juanjorojash/cell_tester_public/charger_discharger.h

/**
 * @file charger_discharger.h
 * @author Juan J. Rojas
 * @date 7 Aug 2018
 * @brief State machine header file for Charge and Discharge System.
 * @par Institution:
 * LaSEINE / CeNT. Kyushu Institute of Technology.
 * @par Mail (after leaving Kyutech):
 * juan.rojas@tec.ac.cr
 * @par Git repository:
 * https://bitbucket.org/juanjorojash/cell_charger_discharger
 */

#ifndef CHARGER_DISCHARGER_H
    #define CHARGER_DISCHARGER_H
    // PIC16F1786 Configuration Bit Settings

    // 'C' source line config statements
    #pragma config FOSC = INTOSC    // Oscillator Selection (INTOSC oscillator: I/O function on CLKIN pin)
    #pragma config WDTE = OFF       // Watchdog Timer Disabled (WDT disabled)
    #pragma config PWRTE = OFF      // Power-up Timer Enable (PWRT disabled)
    #pragma config MCLRE = ON       // MCLR Pin Function Select (MCLR/VPP pin function is MCLR)//If this is enabled, the Timer0 module will not work properly.
    #pragma config CP = OFF         // Flash Program Memory Code Protection (Program memory code protection is disabled)
    #pragma config CPD = OFF        // Data Memory Code Protection (Data memory code protection is disabled)
    #pragma config BOREN = OFF      // Brown-out Reset Enable (Brown-out Reset enabled)
    #pragma config CLKOUTEN = ON    // Clock Out Negative Enable (CLKOUT function is disabled. I/O or oscillator function on the CLKOUT pin)
    #pragma config IESO = ON        // Internal/External Switchover (Internal/External Switchover mode is enabled)
    #pragma config FCMEN = ON       // Fail-Safe Clock Monitor Enable (Fail-Safe Clock Monitor is enabled)

    // CONFIG2
    #pragma config WRT = OFF        // Flash Memory Self-Write Protection (Write protection off)
    #pragma config VCAPEN = OFF     // Voltage Regulator Capacitor Enable bit (Vcap functionality is disabled on RA6.)
    #pragma config PLLEN = OFF      // PLL Enable (4x PLL disabled)
    #pragma config STVREN = ON      // Stack Overflow/Underflow Reset Enable (Stack Overflow or Underflow will cause a Reset)
    #pragma config BORV = LO        // Brown-out Reset Voltage Selection (Brown-out Reset Voltage (Vbor), low trip point selected.)
    #pragma config LPBOR = OFF      // Low Power Brown-Out Reset Enable Bit (Low power brown-out is disabled)
    #pragma config LVP = OFF        // Low-Voltage Programming Enable (Low-voltage programming disabled)//IF THIS IN ON MCLR is always enabled

    #include <xc.h>
    #include <stdio.h>
    #include <stdlib.h>
    #include <math.h>
    #include <stdint.h> // To include uint8_t and uint16_t
    #include <string.h>
    #include <stdbool.h> // Include bool type
    /** This is the State Machine enum*/
	enum states { 
        STANDBY = 0, ///< "Stand by" state, defined by function @link fSTANDBY() @endlink
        IDLE = 1, ///< "Idle" state, defined by function @link fIDLE() @endlink
        FAULT = 2, ///< "Fault" state, defined by function @link fFAULT() @endlink
        ISDONE = 3, ///< "Is done" state, defined by function @link fISDONE() @endlink
        WAIT = 4, ///< "Wait" state, defined by function @link fWAIT() @endlink
        PREDISCHARGE = 5, ///< "Predischarge" state, defined by function @link fDISCHARGE() @endlink
        CHARGE = 6, ///< "Charge" state, defined by function @link fCHARGE() @endlink
        DISCHARGE = 7, ///< "Discharge" state, defined by function @link fDISCHARGE() @endlink
        POSTCHARGE = 8, ///< "Postcharge" state, defined by function @link fCHARGE() @endlink
        DS_DC_res = 9, ///< "Discharged state DC resistance" state, defined by function @link fDC_res() @endlink
        CS_DC_res = 10, ///< "Charged state DC resistance" state, defined by function @link fDC_res() @endlink
        PS_DC_res = 11 ///< "Postcharged state DC resistance" state, defined by function @link fDC_res() @endlink
    };    
    void fSTANDBY(void);
    void fIDLE(void);
    void fCHARGE(void);
    void fDISCHARGE(void);
    void fDC_res(void);
    void fWAIT(void);
    void fISDONE(void);
    void fFAULT(void);
    void start_state_machine(void);
    void state_machine(void);
    void param(void);
    void converter_settings(void);
    void initialize(void);
    void pid(uint16_t feedback, uint16_t setpoint, int24_t* acum, uint16_t* duty_cycle);
    void set_DC(uint16_t* duty_cycle);
    uint16_t read_ADC(uint16_t channel);
    void scaling(void);
    void log_control(void);
    void display_value_u(uint16_t value);
    void display_value_s(int16_t value);
    void cc_cv_mode(uint16_t current_voltage, uint16_t reference_voltage, bool CC_mode_status);
    void control_loop(void);
    void calculate_avg(void);
    void interrupt_enable(void);
    void UART_send_char(char bt);
    char UART_get_char(void); 
    void UART_send_string(char* st_pt);
    void temp_protection(void);
    void Cell_ON(void);
    void Cell_OFF(void);
    void timing(void);
    #define     _XTAL_FREQ              32000000 ///< Frequency to coordinate delays, 32 MHz
    #define     ERR_MAX                 1000 ///< Maximum permisible error, useful to avoid ringing
    #define     ERR_MIN                 -1000 ///< Minimum permisible error, useful to avoid ringing
    #define     V_CHAN                  0b01010 ///< Definition of ADC channel for voltage measurements. AN10(RB1) 
    #define     I_CHAN                  0b01100 ///< Definition of ADC channel for current measurements. AN12(RB0)
    #define     T_CHAN                  0b00100 ///< Definition of ADC channel for temperature measurements. AN4(RA5)
    #define     CELL1_ON()              { RB2 = 1; } ///< Turn on Cell #1
    #define     CELL2_ON()              { RB3 = 1; } ///< Turn on Cell #2
    #define     CELL3_ON()              { RB4 = 1; } ///< Turn on Cell #3
    #define     CELL4_ON()              { RB5 = 1; } ///< Turn on Cell #4
    #define     CELL1_OFF()             { RB2 = 0; } ///< Turn off Cell #1
    #define     CELL2_OFF()             { RB3 = 0; } ///< Turn off Cell #2
    #define     CELL3_OFF()             { RB4 = 0; } ///< Turn off Cell #3
    #define     CELL4_OFF()             { RB5 = 0; } ///< Turn off Cell #4
    #define     AD_SET_CHAN(x)          { ADCON0bits.CHS = x; __delay_us(5); } ///< Set the ADC channel to @p x and wait for 5 microseconds.
    #define     AD_CONVERT()            { GO_nDONE = 1; while(GO_nDONE);} ///< Start the conversion and wait until it is finished
    #define     AD_RESULT()             { ad_res = 0; ad_res = (ADRESL & 0xFF)|((ADRESH << 8) & 0xF00);} ///< Store conversion result in #ad_res
    /** @brief Stop the converter*/
    /** Set @p conv to zero, turn off the main relay (@p RC5), set the duty cycle in @p DC_MIN, 
    turn off all the cell relays in the switcher board, disable the logging of data to the terminal 
    and the UART reception interrupts.
    */
    #define     STOP_CONVERTER()        { RC3 = 0; RC4 = 0; conv = 0; RC5 = 0; dc = DC_MIN; set_DC(&dc); Cell_OFF(); LOG_OFF();}
    #define     UART_INT_ON()           { while(RCIF) clear = RC1REG; RCIE = 1; } ///< Clear transmission buffer and turn ON UART transmission interrupts.
    #define     LOG_ON()                { log_on = 1; }  ///< Turn OFF logging in the terminal.
    #define     LOG_OFF()               { log_on = 0; }  ///< Turn ON logging in the terminal.
    #define     RESET_TIME()            { minute = 0; second = -1; } ///< Reset timers.
   //It seems that above 0.8 of DC the losses are so high that I don't get anything similar to the transfer function 
    #define     DC_MIN                  50  ///< Minimum possible duty cycle, set around @b 0.1 
    #define     DC_MAX                  409  ///< Maximum possible duty cycle, set around @b 0.8
    #define     COUNTER                 1024  ///< Counter value, needed to obtained one second between counts.
    #define     CC_char_kp              20  ///< Proportional constant divider for CC mode
    #define     CC_char_ki              50  ///< Integral constant divider for CC mode 
    #define     CC_disc_kp              15  ///< Proportional constant divider for CC mode
    #define     CC_disc_ki              20  ///< Integral constant divider for CC mode 
    // last test with LI_ION gave this constants
    #define     CV_kp                   5  ///< Proportional constant divider for CV mode
    #define     CV_ki                   20  ///< Integral constant divider for CV mode 
    #define     LINEBREAK               { UART_send_char(10); UART_send_char(13); } ///< Send a linebreak to the terminal
    //////////////////////////Chemistry definition///////////////////////////////////////
    #define     LI_ION_CHEM             1 ///< Set this definition to 1 and NI_MH_CHEM to 0 to set the test Li-Ion cells  
    #define     NI_MH_CHEM              0 ///< Set this definition to 1 and LI_ION_CHEM to 0 to set the test Ni-MH cells
    ////////////////////////////////////////////////////////////////////////////////////
    //General definitions
    #define     WAIT_TIME               60 ///< Time to wait before states, set to 10 minutes
    #define     DC_RES_SECS             14 ///< How many seconds the DC resistance process takes
    //Li-Ion definitions
    #define     Li_Ion_CV               4200 ///< Li-Ion constant voltage setting in mV
    #define     Li_Ion_CAP              3250 ///< Li-Ion capacity setting in mAh
    #define     Li_Ion_EOC_I            100 ///< Li-Ion end-of-charge current in mA
    #define     Li_Ion_EOD_V            3000 ///< Li_Ion end-of-discharge voltage in mV
//    //HACK FOR LI-PO (make system thinks it is Li-Ion)
//    #define     Li_Ion_CV               4200 ///< Li-Ion constant voltage setting in mV
//    #define     Li_Ion_CAP              1200 ///< Li-Ion capacity setting in mAh
//    #define     Li_Ion_EOC_I            60 ///< Li-Ion end-of-charge current in mA
//    #define     Li_Ion_EOD_V            3000 ///< Li_Ion end-of-discharge voltage in mV
//    //Li-Po definitions
//    #define     Li_Po_CV                4200 ///< Li-Ion constant voltage setting in mV
//    #define     Li_Po_CAP               1200 ///< Li-Ion capacity setting in mAh
//    #define     Li_Po_EOC_I             60 ///< Li-Ion end-of-charge current in mA
//    #define     Li_Po_EOD_V             3000 ///< Li_Ion end-of-discharge voltage in mV
    //Ni-MH definitions
    #define     Ni_MH_CV                1750 ///< Ni-MH constant voltage setting in mV
    #define     Ni_MH_CAP               2000 ///< Ni-MH capacity setting in mAh
    #define     Ni_MH_EOC_DV            10 ///< Ni-MH end-fo-charge voltage drop in mV
    #define     Ni_MH_EOD_V             1000 ///< Ni-MH end-of-discharge voltage in mV

    #define     SET_DISC()              { RC3 = 0; RC4 = 0; __delay_ms(100); RC3 = 1; __delay_ms(100); RC3 = 0; __delay_ms(100); RC5 = 1; __delay_ms(100); kp = CC_disc_kp; ki = CC_disc_ki;}
    #define     SET_CHAR()              { RC3 = 0; RC4 = 0; __delay_ms(100); RC4 = 1; __delay_ms(100); RC4 = 0; __delay_ms(100); RC5 = 1; __delay_ms(100); kp = CC_char_kp; ki = CC_char_ki;}
    //Variables
    bool                                SECF = 1; ///< 1 second flag
    unsigned char                       option = 0; ///< Four different options, look into @link param() @endlink for details
    uint16_t                            capacity; ///< Definition of capacity per cell according to each chemistry
    uint16_t                            i_char; ///< Charging current in mA
    uint16_t                            i_disc; ///< Discharging current in mA
    unsigned char                       cell_count = 1; ///< Cell counter from '1' to '4'. Initialized as '1'
    unsigned char                       cell_max = 0; ///< Number of cells to be tested. Initialized as 0
    uint16_t                            wait_count = 0; ///< Counter for waiting time between states. Initialized as 0
    unsigned char                       dc_res_count = 0; ///< Counter for DC resistance. Initialized as 0
    unsigned char                       state = STANDBY; ///< Used with store the value of the @link states @endlink enum. Initialized as @link STANDBY @endlink
    unsigned char                       prev_state = STANDBY; ///< Used to store the previous state. Initialized as @link STANDBY @endlink  
    uint16_t                            EOC_current; ///< End-of-charge current in mA
    uint16_t                            EOD_voltage; ///< End-of-dischage voltage in mV
    uint16_t                            v_1_dcres; ///< First voltage measured during DC resistance state 
    uint16_t                            i_1_dcres; ///< First current measured during DC resistance state  
    uint16_t                            v_2_dcres; ///< Second voltage measured during DC resistance state 
    uint16_t                            i_2_dcres; ///< Second current measured during DC resistance state
    uint24_t                            dc_res_val; ///< To store the operation of obtained from the DC resistance state
    bool                                conv = 0; ///< Turn controller ON(1) or OFF(0). Initialized as 0
    uint16_t                            count = COUNTER; ///< Counter that should be cleared every second. Initialized as #COUNTER 
    /**< Every control loop cycle this counter will be decreased. This variable is used to calculate the averages and to trigger
    all the events that are done every second.*/
    //uint16_t                            ad_res; ///< Result of an ADC measurement.
    uint16_t                            v;  ///< Last voltage ADC measurement.
    uint16_t                            i;  ///< Last current ADC measurement.
    uint16_t                            t;  ///<  Last temperature ADC measurement.
    uint24_t                            vacum = 0; ///< accumulator dor v
    uint24_t                            iacum = 0;
    uint24_t                            tacum = 0;
    //qavg does not need accumulator
    uint16_t                            vavg = 0;  ///< Last one-second-average of #v . Initialized as 0
    uint16_t                            iavg = 0;  ///< Last one-second-average of #i . Initialized as 0
    int16_t                             tavg = 0;  ///< Last one-second-average of #t . Initialized as 0
    uint16_t                            qavg = 0;  ///< Integration of #i . Initialized as 0
    uint16_t                            vmax = 0;   ///< Maximum recorded average voltage. 
    int24_t                             intacum;   ///< Integral acumulator of PI compensator
    float                               kp;  ///< Proportional compesator gain
    float                               ki;  ///< Integral compesator gain      
    uint16_t                            vref = 0;  ///< Scaled voltage setpoint. Initialized as 0
    uint16_t                            cvref = 0;  ///< Unscaled voltage setpoint. Initialized as 0
    uint16_t                            iref = 0;  ///< Current setpoint. Initialized as 0
    uint16_t                            ccref = 0;  ///< Unscaled voltage setpoint. Initialized as 0
    bool                                cmode = 1;  ///< CC / CV selector. CC: <tt> cmode = 1 </tt>. CV: <tt> cmode = 0 </tt>   
    uint16_t                            dc = 0;  ///< Duty cycle
    //char                                clear;  ///< Variable to clear the transmission buffer of UART
    bool                                log_on = 0; ///< Variable to indicate if the log is activated 
    int16_t                             second = 0; ///< Seconds counter, resetted after 59 seconds.
    uint16_t                            minute = 0; ///< Minutes counter, only manually reset
    uint16_t                            timeout = 0;
    //Strings       
    char const                          comma = ',';
    char const                          colons = ':'; 
    char const                          S_str = 'S';
    char const                          C_str = 'C';
    char const                          V_str = 'V';
    char const                          I_str = 'I';
    char const                          T_str = 'T';
    char const                          Q_str = 'Q';
    char const                          R_str = 'R';
    char const                          W_str = 'W';
    char const                          press_s_str[] = "'s' to start: ";
    char const                          starting_str[] = "starting...";
    char const                          input_num_str[] = "Input a number between";
    char const                          param_def_str[] = "Parameter definition:";
    char const                          re_str[] = "re";
    char const                          chem_def_liion[] = "Li-Ion";
    char const                          chem_def_nimh[] = "Ni-MH";
    char const                          mV_str[] = " mV";
    char const                          mAh_str[] = " mAh";
    char const                          mA_str[] = " mA";
    char const                          EOD_V_str[] = "EOD: ";
    char const                          EOC_I_str[] = "EOC: ";
    char const                          EOC_DV_str[] = "EOC DV: ";
    char const                          cho_bet_str[] = "Chose: ";
    char const                          quarter_c_str[] = "0.25C";
    char const                          half_c_str[] = "0.50C";
    char const                          one_c_str[] = "1C";
    char const                          cell_str[] = "Cell "; 
    char const                          dis_def_str[] = "Discharge current: ";
    char const                          char_def_str[] = "Charge current: ";
    char const                          cv_val_str[] = "CV: ";
    char const                          nom_cap_str[] = "Capacity: ";
    char const                          def_char_curr_str[] = "Charge current: ";
    char const                          def_disc_curr_str[] = "Discharge current: ";
    char const                          num_cell_str[] = "Number of cells: ";
    char const                          one_str[] = "1) ";
    char const                          two_str[] = "2) ";
    char const                          three_str[] = "3) ";
    char const                          four_str[] = "4) ";
    char const                          op_1_str[] = "Predischarge->Charge->Discharge->Postcharge";
    char const                          op_2_str[] = "Charge->Discharge";
    char const                          op_3_str[] = "Only Charge";
    char const                          op_4_str[] = "Only Discharge";
    char const                          sel_str[] = " selected...";
    char const                          cell_below_str[] = "Cell below 0.9V or not present";

#endif /* CHARGER_DISCHARGER_H*/
